2ELE088-ProjetoIntegrador3B-T3T4/Grupo4-TecladoNumerico/teclado/Modelo 3D/swith.STEP

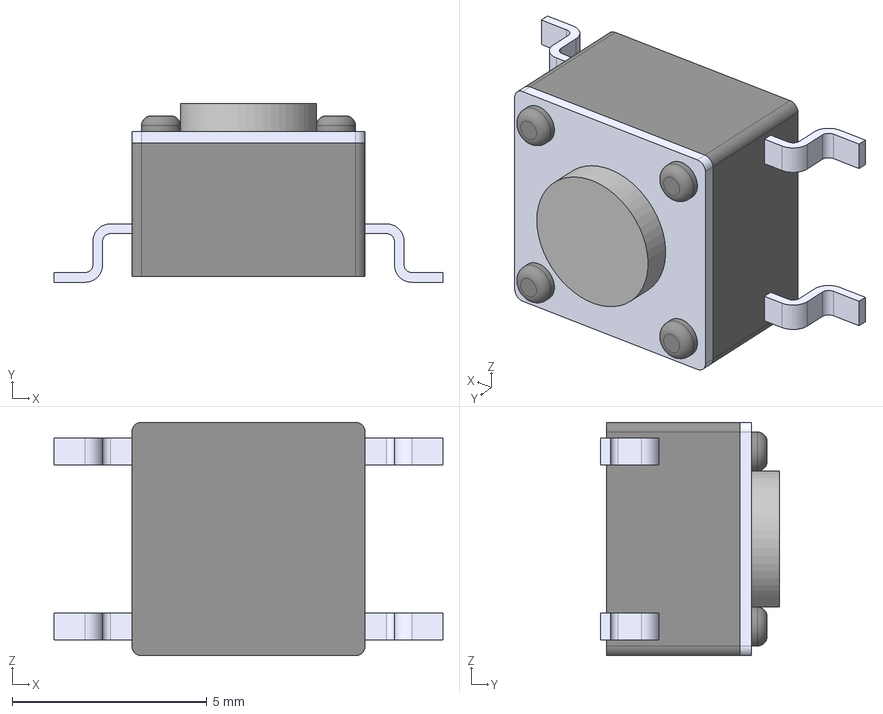
[picture p15: CAD file, 2025-11-06]
teclado/Modelo 3D/swith.STEP
10.0 x 4.59 x 6.00 mm
Body003 (Mirror #1)
Body003 (Mirror #3)
Body003 (Mirror #2)
