2ELE088-ProjetoIntegrador3B-T3T4/Grupo4-TecladoNumerico/teclado/Modelo 3D/Switche.STEP

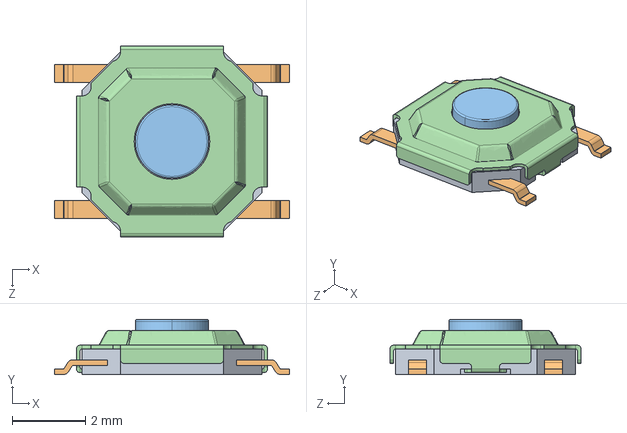
[picture p16: CAD file, 2025-11-06]
teclado/Modelo 3D/Switche.STEP
6.40 x 1.50 x 5.20 mm
