2ELE088-ProjetoIntegrador3B-T3T4/Grupo4-TecladoNumerico/teclado/Modelo 3D/fuse.STEP

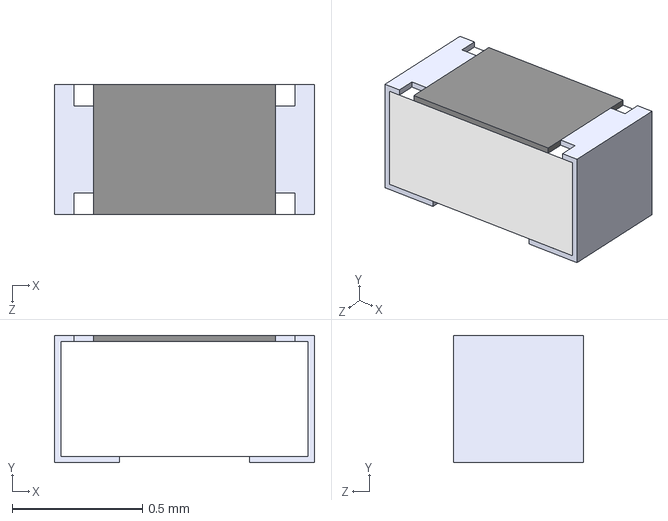
[picture p17: CAD file, 2025-11-06]
teclado/Modelo 3D/fuse.STEP
1 x 0.49 x 0.5 mm
