2ELE088-ProjetoIntegrador3B-T3T4/Grupo4-TecladoNumerico/teclado/Modelo 3D/resistor 510r 0603.stp

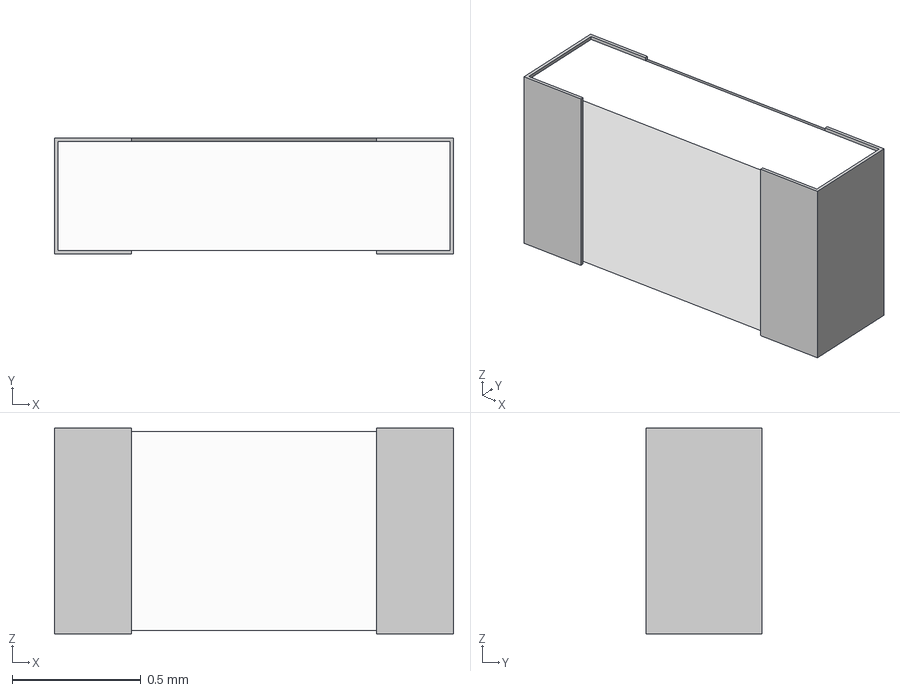
[picture p18: CAD file, 2025-11-06]
teclado/Modelo 3D/resistor 510r 0603.stp
1.55 x 0.45 x 0.8 mm
