2ELE088-ProjetoIntegrador3B-T3T4/Grupo4-TecladoNumerico/teclado/Modelo 3D/Diodo.STEP

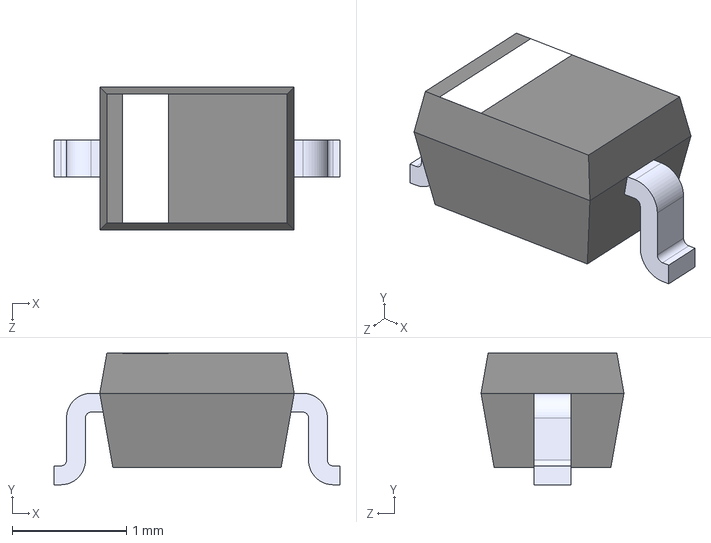
[picture p19: CAD file, 2025-11-06]
teclado/Modelo 3D/Diodo.STEP
2.50 x 1.15 x 1.25 mm
