2ELE088-ProjetoIntegrador3B-T3T4/Grupo4-TecladoNumerico/teclado/Modelo 3D/R 1.5k 0402.step

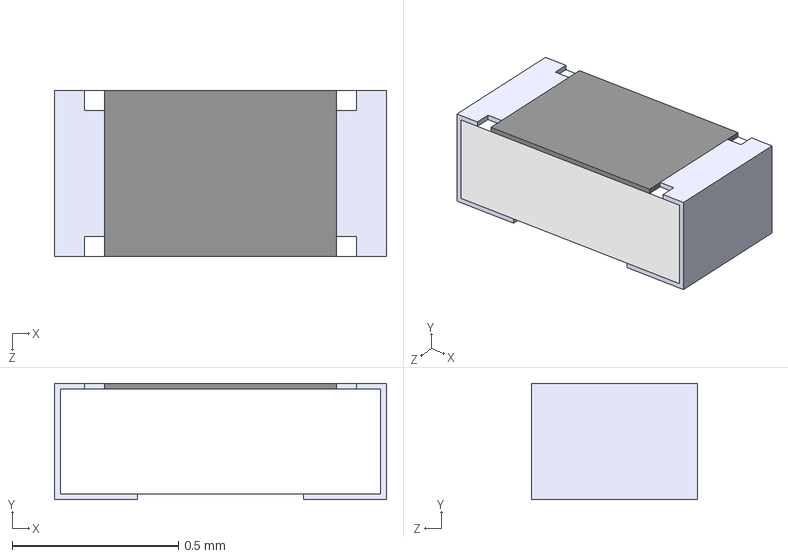
[picture p20: CAD file, 2025-11-06]
teclado/Modelo 3D/R 1.5k 0402.step
1 x 0.35 x 0.5 mm
