2ELE088-ProjetoIntegrador3B-T3T4/Grupo4-TecladoNumerico/teclado/Modelo 3D/resistor 100k 0603.step

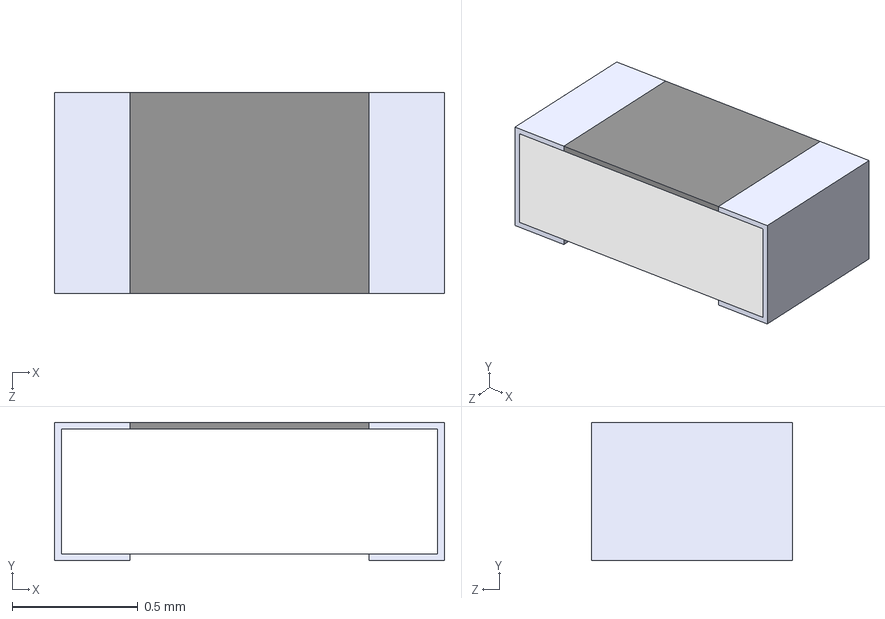
[picture p21: CAD file, 2025-11-06]
teclado/Modelo 3D/resistor 100k 0603.step
1.55 x 0.55 x 0.8 mm
