2ELE088-ProjetoIntegrador3B-T3T4/Grupo4-TecladoNumerico/teclado/Modelo 3D/cristal 32,768k.STEP

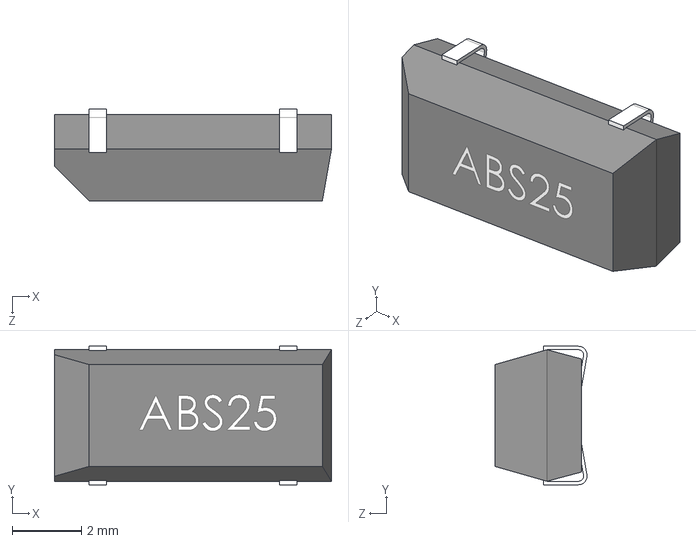
[picture p22: CAD file, 2025-11-06]
teclado/Modelo 3D/cristal 32,768k.STEP
8.00 x 4.00 x 2.66 mm
