2ELE088-ProjetoIntegrador3B-T3T4/Grupo4-TecladoNumerico/teclado/Modelo 3D/cristal 8MHZ.STEP

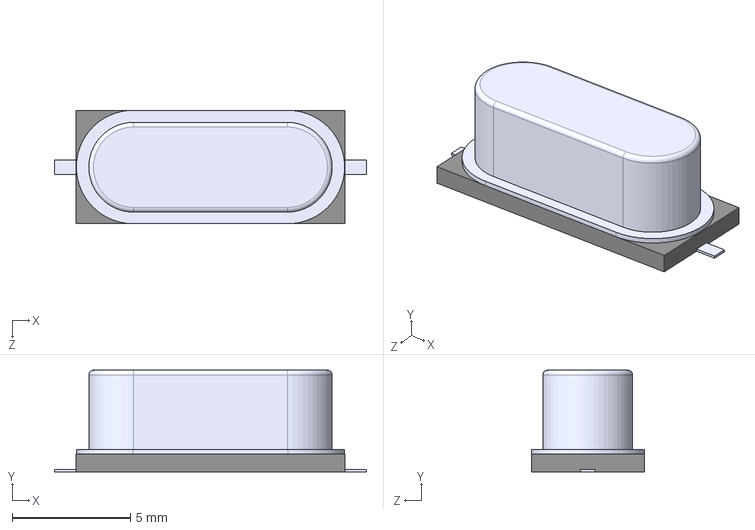
[picture p23: CAD file, 2025-11-06]
teclado/Modelo 3D/cristal 8MHZ.STEP
13.2 x 4.30 x 4.80 mm
