2ELE088-ProjetoIntegrador3B-T3T4/Grupo4-TecladoNumerico/teclado/Modelo 3D/conector 3x2.stp

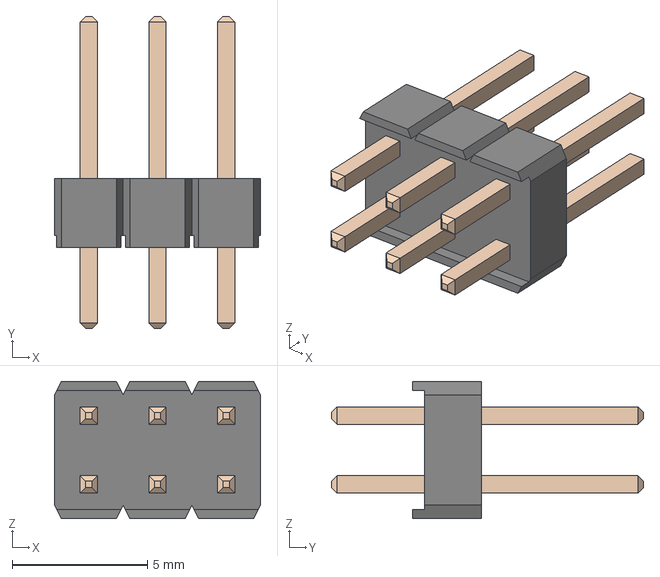
[picture p25: CAD file, 2025-11-06]
teclado/Modelo 3D/conector 3x2.stp
7.62 x 11.5 x 5.08 mm
6130xx21121_PIN x 6
