2ELE088-ProjetoIntegrador3B-T3T4/Grupo4-TecladoNumerico/teclado/Modelo 3D/R 1m 0603.step

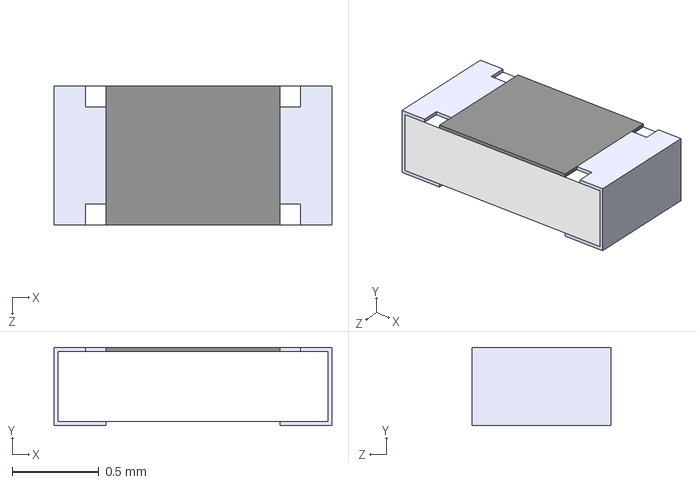
[picture p26: CAD file, 2025-11-06]
teclado/Modelo 3D/R 1m 0603.step
1.60 x 0.45 x 0.8 mm
