2ELE088-ProjetoIntegrador3B-T3T4/Grupo4-TecladoNumerico/teclado/Modelo 3D/micro usb.STEP

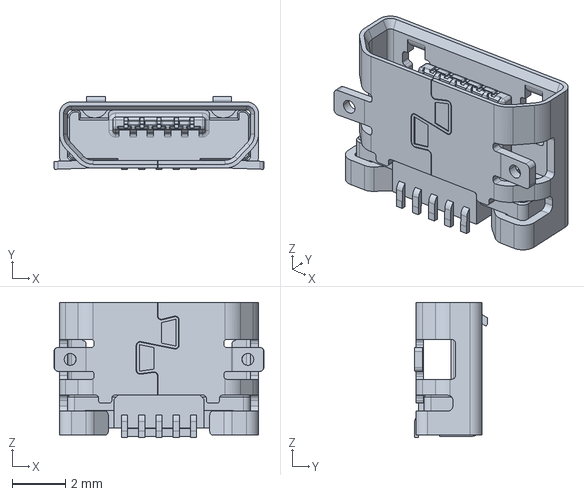
[picture p27: CAD file, 2025-11-06]
teclado/Modelo 3D/micro usb.STEP
7.91 x 2.77 x 5.10 mm
