2ELE088-ProjetoIntegrador3B-T3T4/Grupo4-TecladoNumerico/teclado/Modelo 3D/STM32F103C8T6.STEP

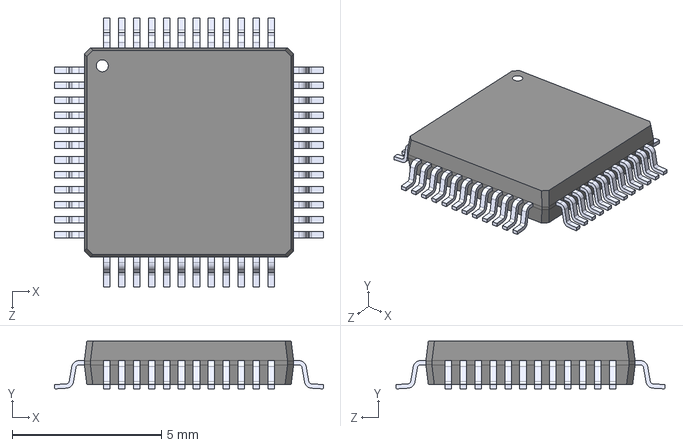
[picture p29: CAD file, 2025-11-06]
teclado/Modelo 3D/STM32F103C8T6.STEP
9.00 x 1.60 x 9.00 mm
