2ELE088-ProjetoIntegrador3B-T3T4/Grupo4-TecladoNumerico/teclado/Modelo 3D/conctor angulado.STEP

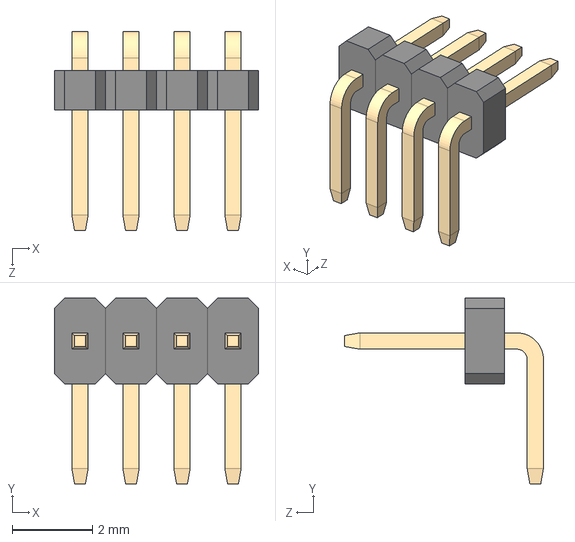
[picture p30: CAD file, 2025-11-06]
teclado/Modelo 3D/conctor angulado.STEP
5.08 x 4.62 x 4.95 mm
GRPB041VWCN-RC_GRPB04
Pin - Gold x 4
