2ELE088-ProjetoIntegrador3B-T3T4/Grupo4-TecladoNumerico/teclado/Modelo 3D/cap 106 0603.step

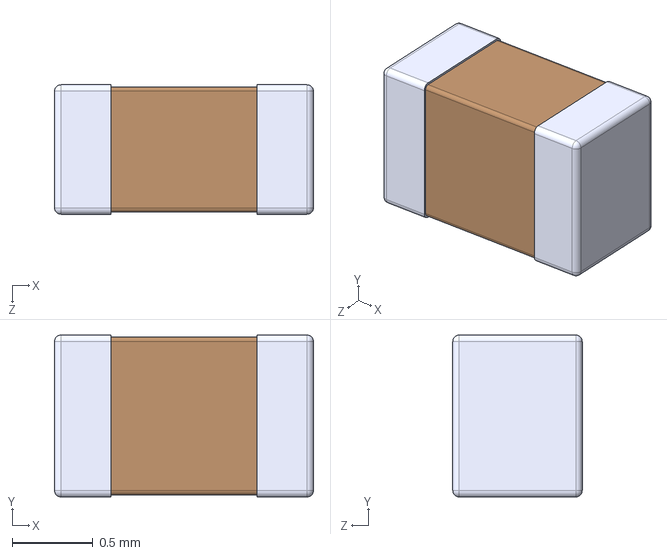
[picture p31: CAD file, 2025-11-06]
teclado/Modelo 3D/cap 106 0603.step
1.60 x 1.00 x 0.8 mm
