2ELE088-ProjetoIntegrador3B-T3T4/Grupo4-TecladoNumerico/teclado/Modelo 3D/led branco.STEP

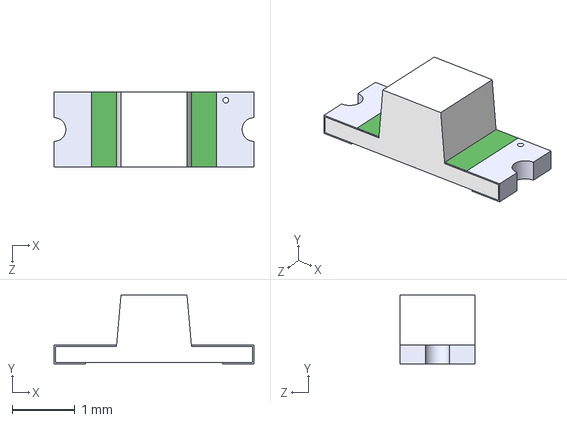
[picture p32: CAD file, 2025-11-06]
teclado/Modelo 3D/led branco.STEP
3.20 x 1.10 x 1.20 mm
