2ELE088-ProjetoIntegrador3B-T3T4/Grupo4-TecladoNumerico/teclado/Modelo 3D/suporte HS.stp

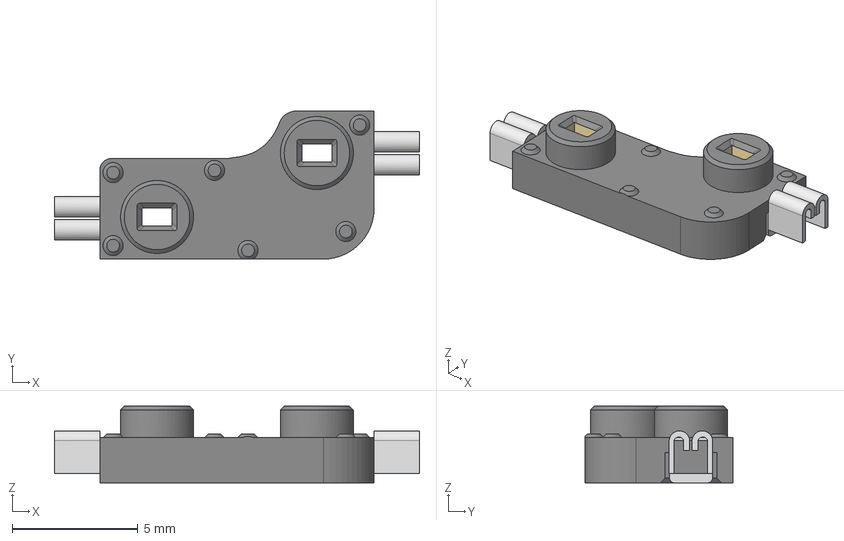
[picture p33: CAD file, 2025-11-06]
teclado/Modelo 3D/suporte HS.stp
14.5 x 5.89 x 3.05 mm
