2ELE088-ProjetoIntegrador3B-T3T4/Grupo4-TecladoNumerico/teclado/Modelo 3D/CRCW060310K0FKEA.STEP

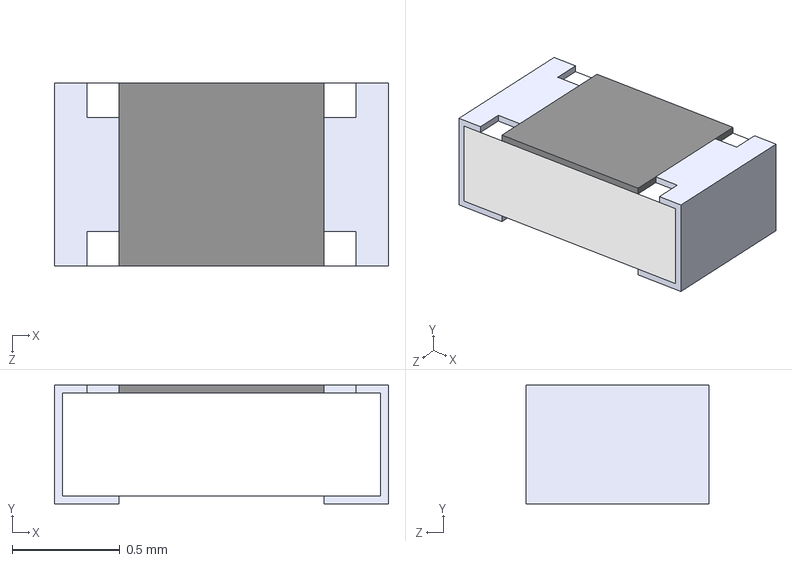
[picture p34: CAD file, 2025-11-06]
teclado/Modelo 3D/CRCW060310K0FKEA.STEP
1.55 x 0.55 x 0.85 mm
