2ELE088-ProjetoIntegrador3B-T3T4/Grupo4-TecladoNumerico/teclado/Modelo 3D/Protetor curto.step

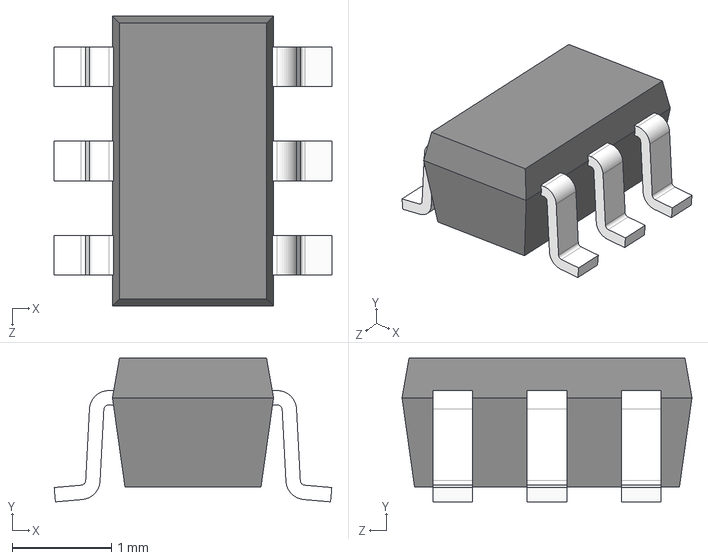
[picture p36: CAD file, 2025-11-06]
teclado/Modelo 3D/Protetor curto.step
2.80 x 1.45 x 2.92 mm
