2ELE088-ProjetoIntegrador3B-T3T4/Grupo4-TecladoNumerico/teclado/Modelo 3D/USBC.stp

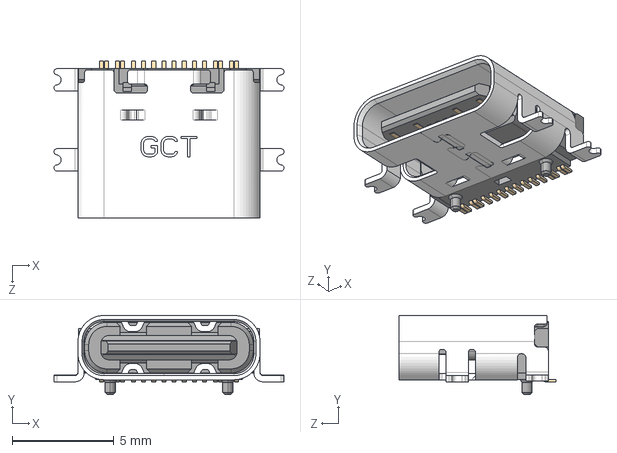
[picture p37: CAD file, 2025-11-06]
teclado/Modelo 3D/USBC.stp
11.3 x 3.89 x 7.70 mm
