2ELE088-ProjetoIntegrador3B-T3T4/Grupo4-TecladoNumerico/teclado/Modelo 3D/regulador.STEP

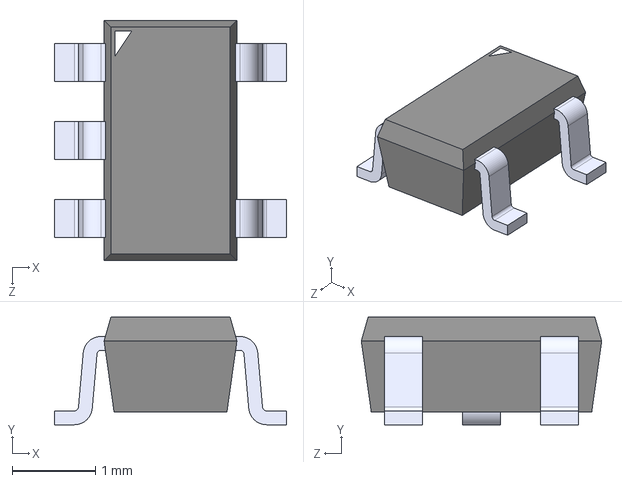
[picture p38: CAD file, 2025-11-06]
teclado/Modelo 3D/regulador.STEP
2.79 x 1.30 x 2.90 mm
